atsuyuki/dactyl-manuform-skeleton-edition-4x5/img/image1.png

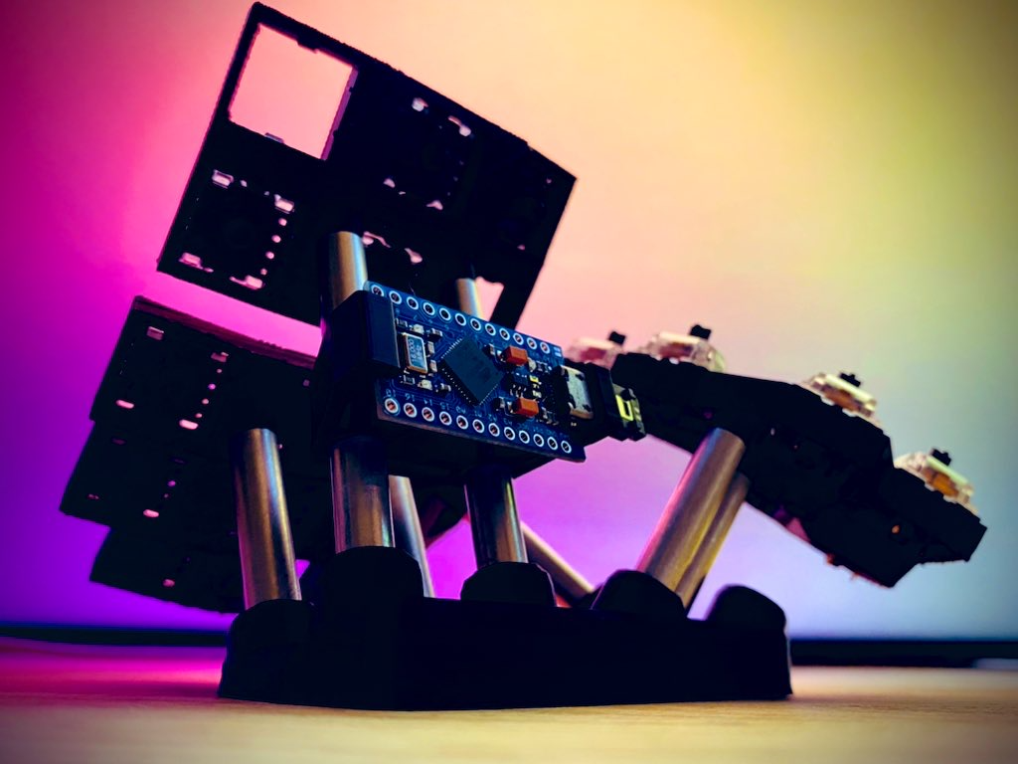
img/image1.png
