atsuyuki/dactyl-manuform-skeleton-edition-4x5/img/image2.png

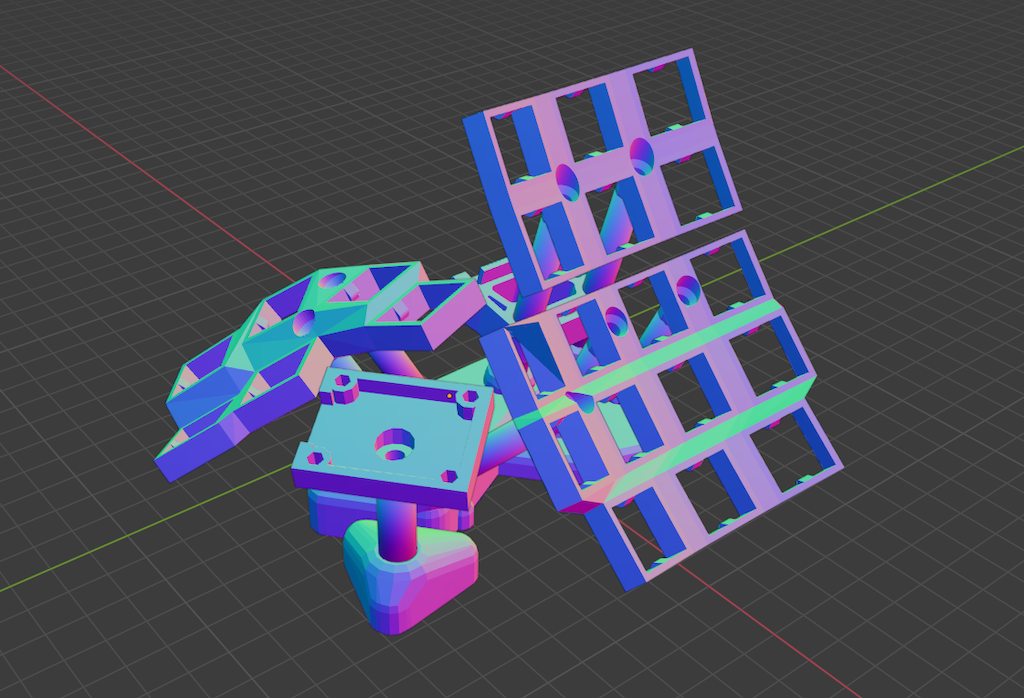
img/image2.png
