atsuyuki/dactyl-manuform-skeleton-edition-4x5/things/right_top.stl

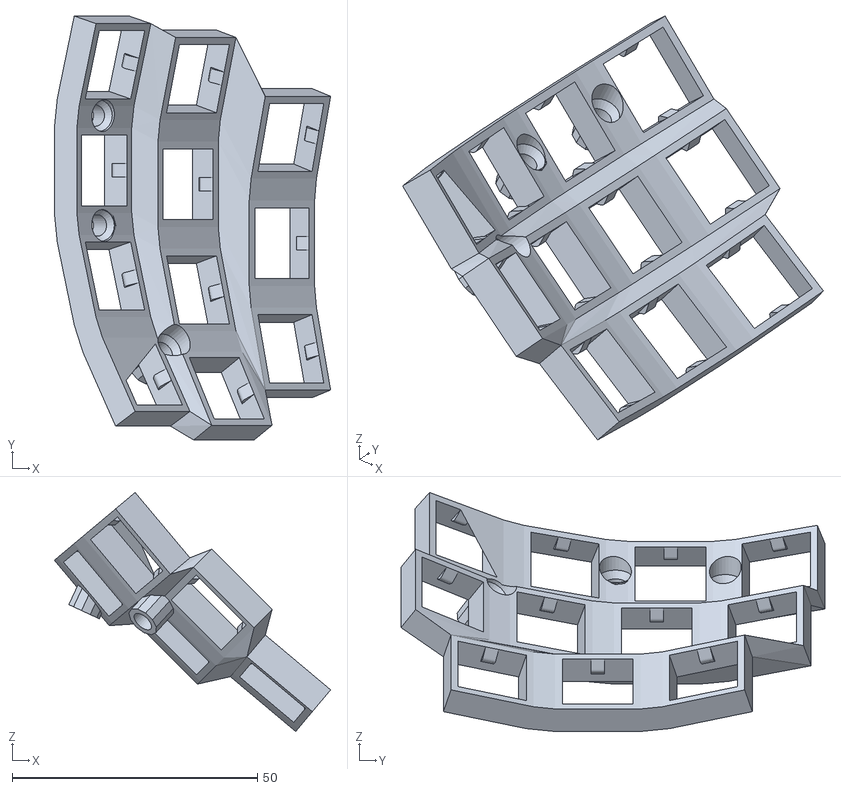
[picture p20: CAD file, 2021-04-04]
things/right_top.stl
56.3 x 86.4 x 48.7
