atsuyuki/dactyl-manuform-skeleton-edition-4x5/source/joystick/right_model.stl

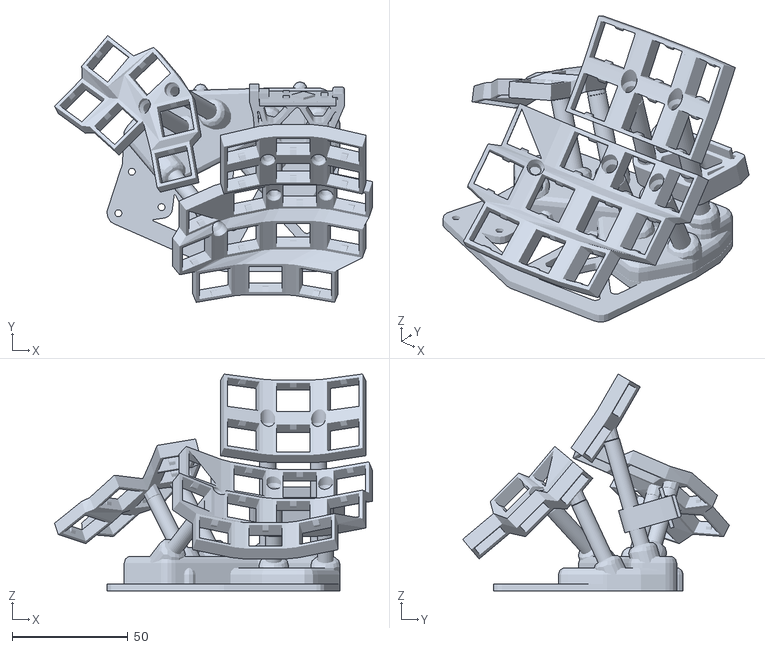
[picture p21: CAD file, 2021-06-23]
source/joystick/right_model.stl
137.5 x 115.4 x 93.8
