atsuyuki/dactyl-manuform-skeleton-edition-4x5/source/things/right-5x6-plate-ready-to-cut.dxf

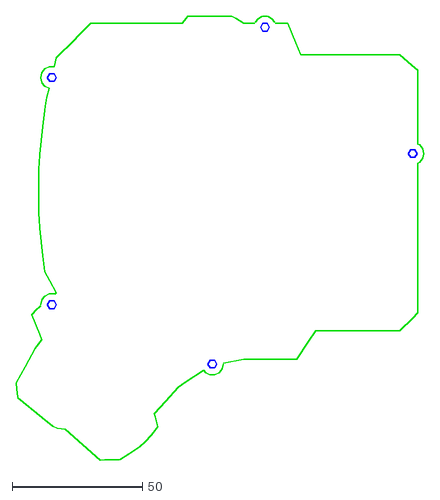
[picture p22: CAD file, 2021-04-20]
source/things/right-5x6-plate-ready-to-cut.dxf
156.5 x 170.5
