atsuyuki/dactyl-manuform-skeleton-edition-4x5/things/right_index.stl

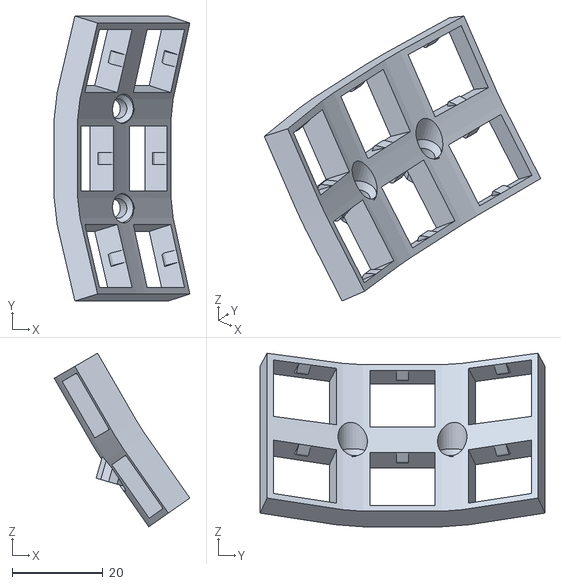
[picture p23: CAD file, 2021-04-04]
things/right_index.stl
30.0 x 63.0 x 38.4
