atsuyuki/dactyl-manuform-skeleton-edition-4x5/source/joystick/clay_model_fixed.stl

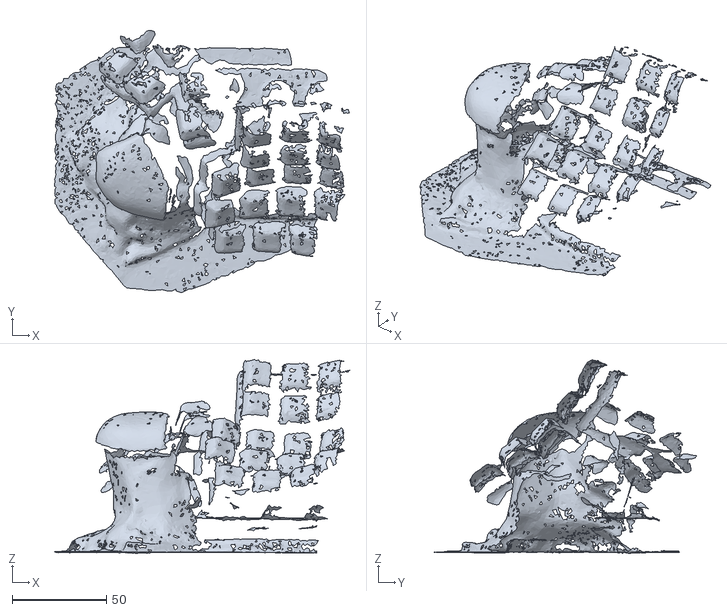
[picture p24: CAD file, 2021-06-23]
source/joystick/clay_model_fixed.stl
156.5 x 139.2 x 103.2
