atsuyuki/dactyl-manuform-skeleton-edition-4x5/source/things/right-4x6-plate.dxf

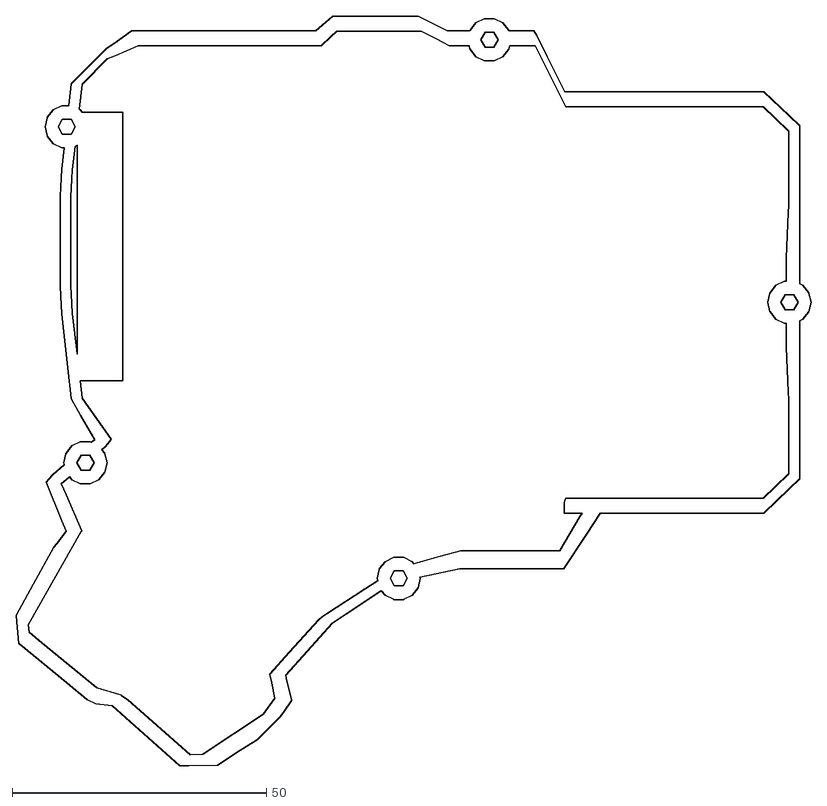
[picture p25: CAD file, 2021-04-20]
source/things/right-4x6-plate.dxf
156.5 x 147.5
