atsuyuki/dactyl-manuform-skeleton-edition-4x5/things/right_bottom.stl

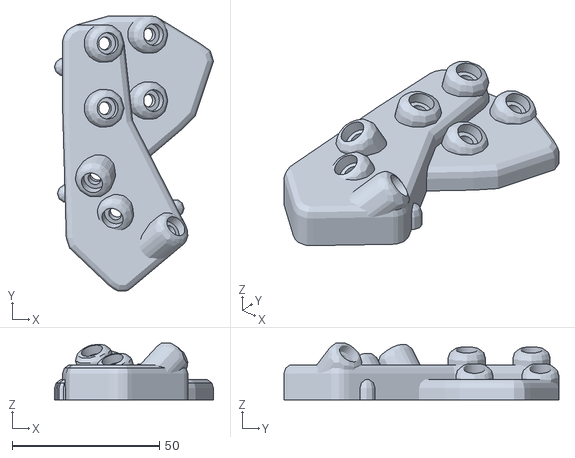
[picture p26: CAD file, 2021-04-04]
things/right_bottom.stl
54.0 x 93.4 x 19.3
