atsuyuki/dactyl-manuform-skeleton-edition-4x5/source/joystick/joystick v10.obj

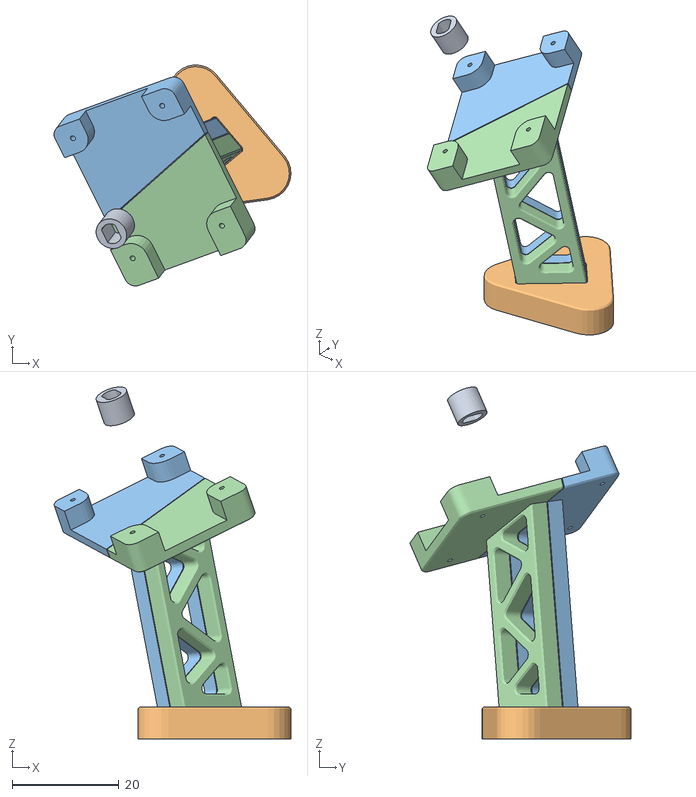
[picture p27: CAD file, 2021-06-23]
source/joystick/joystick v10.obj
44.4 x 41.4 x 66.0
