atsuyuki/dactyl-manuform-skeleton-edition-4x5/source/things/right-plate.dxf

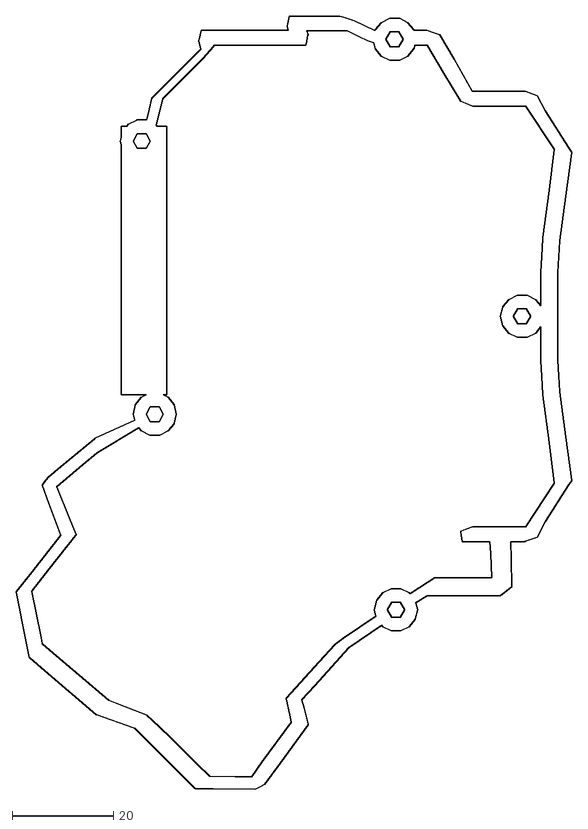
[picture p28: CAD file, 2021-04-20]
source/things/right-plate.dxf
109.4 x 152.3
