atsuyuki/dactyl-manuform-skeleton-edition-4x5/source/things/right-4x5-plate.dxf

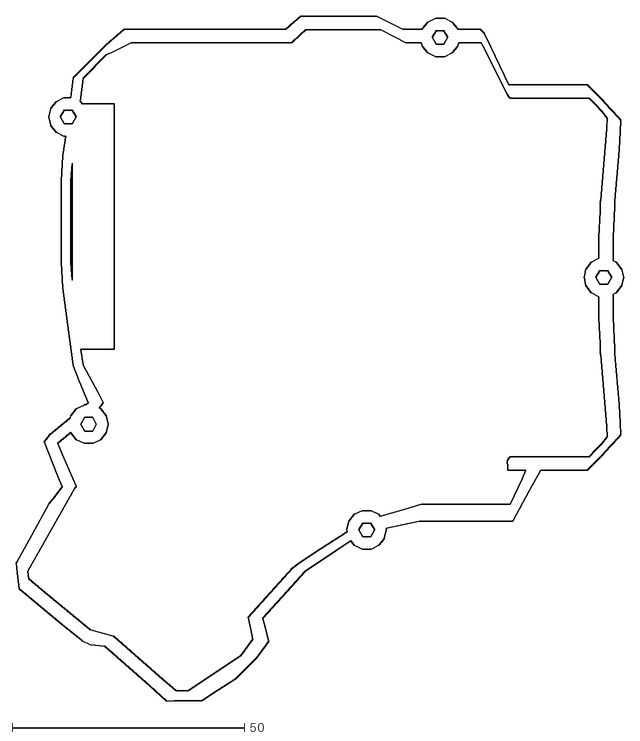
[picture p29: CAD file, 2021-04-20]
source/things/right-4x5-plate.dxf
130.7 x 147.5
