atsuyuki/dactyl-manuform-skeleton-edition-4x5/source/joystick/joystick_bracket_bottom.stl

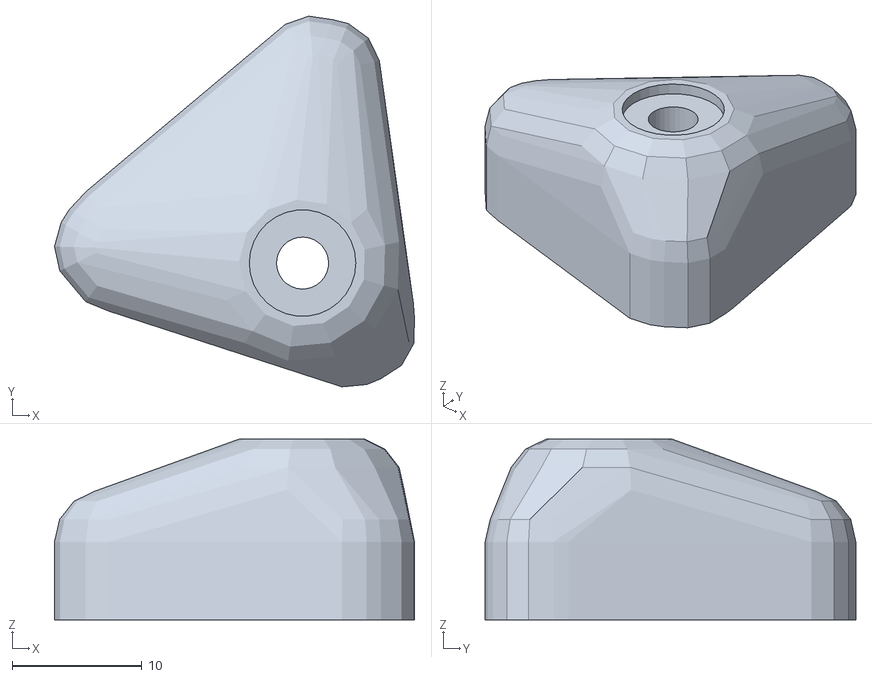
[picture p30: CAD file, 2021-02-26]
source/joystick/joystick_bracket_bottom.stl
27.7 x 28.5 x 13.9
