atsuyuki/dactyl-manuform-skeleton-edition-4x5/source/joystick/joystick_bracket_top.stl

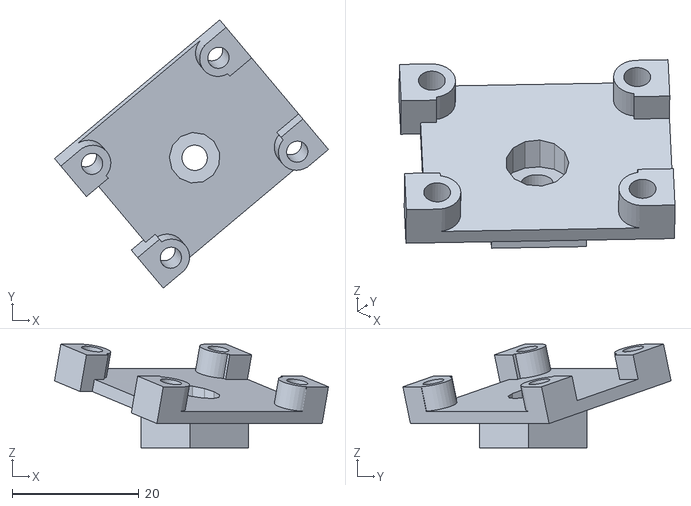
[picture p31: CAD file, 2021-02-26]
source/joystick/joystick_bracket_top.stl
43.2 x 42.3 x 16.4
