atsuyuki/dactyl-manuform-skeleton-edition-4x5/source/things/left_mirror.scad

mirror([1,0,0]){
 import("right_baseplate.stl");
// import("right_bottom.stl");
// import("right_index.stl");
// import("right_thumb.stl");
// import("right_top.stl");
}
