atsuyuki/dactyl-manuform-skeleton-edition-4x5/source/things/right.scad

difference () {
  union () {
    union () {
      translate ([0, 0, 30]) {
        rotate (a=40.0, v=[0, 1, 0]) {
          translate ([0, 0, 0]) {
            translate ([0, 0, 246.80957697923077]) {
              rotate (a=20.0, v=[0, 1, 0]) {
                translate ([0, 0, -246.80957697923077]) {
                  translate ([0, 0, 89.18393769497159]) {
                    rotate (a=14.999999999999998, v=[1, 0, 0]) {
                      translate ([0, 0, -89.18393769497159]) {
                        union () {
                          union () {
                            translate ([0, 7.95, 3]) {
                              cube ([17.4, 1.5, 6], center=true);
                            }
                            translate ([7.95, 0, 3]) {
                              cube ([1.5, 17.4, 6], center=true);
                            }
                            hull () {
                              translate ([7.95, 0, 4.0]) {
                                cube ([1.5, 2.75, 4], center=true);
                              }
                              translate ([7.2, 0, 3.5]) {
                                rotate (a=90.0, v=[1, 0, 0]) {
                                  cylinder ($fn=30, h=2.75, r=0.95, center=true);
                                }
                              }
                            }
                          }
                          mirror ([0, 1, 0]) {
                            mirror ([1, 0, 0]) {
                              union () {
                                translate ([0, 7.95, 3]) {
                                  cube ([17.4, 1.5, 6], center=true);
                                }
                                translate ([7.95, 0, 3]) {
                                  cube ([1.5, 17.4, 6], center=true);
                                }
                                hull () {
                                  translate ([7.95, 0, 4.0]) {
                                    cube ([1.5, 2.75, 4], center=true);
                                  }
                                  translate ([7.2, 0, 3.5]) {
                                    rotate (a=90.0, v=[1, 0, 0]) {
                                      cylinder ($fn=30, h=2.75, r=0.95, center=true);
                                    }
                                  }
                                }
                              }
                            }
                          }
                        }
                      }
                    }
                  }
                }
              }
            }
          }
        }
      }
      translate ([0, 0, 30]) {
        rotate (a=40.0, v=[0, 1, 0]) {
          translate ([0, 0, 0]) {
            translate ([0, 0, 246.80957697923077]) {
              rotate (a=20.0, v=[0, 1, 0]) {
                translate ([0, 0, -246.80957697923077]) {
                  translate ([0, 0, 89.18393769497159]) {
                    rotate (a=0.0, v=[1, 0, 0]) {
                      translate ([0, 0, -89.18393769497159]) {
                        union () {
                          union () {
                            translate ([0, 7.95, 3]) {
                              cube ([17.4, 1.5, 6], center=true);
                            }
                            translate ([7.95, 0, 3]) {
                              cube ([1.5, 17.4, 6], center=true);
                            }
                            hull () {
                              translate ([7.95, 0, 4.0]) {
                                cube ([1.5, 2.75, 4], center=true);
                              }
                              translate ([7.2, 0, 3.5]) {
                                rotate (a=90.0, v=[1, 0, 0]) {
                                  cylinder ($fn=30, h=2.75, r=0.95, center=true);
                                }
                              }
                            }
                          }
                          mirror ([0, 1, 0]) {
                            mirror ([1, 0, 0]) {
                              union () {
                                translate ([0, 7.95, 3]) {
                                  cube ([17.4, 1.5, 6], center=true);
                                }
                                translate ([7.95, 0, 3]) {
                                  cube ([1.5, 17.4, 6], center=true);
                                }
                                hull () {
                                  translate ([7.95, 0, 4.0]) {
                                    cube ([1.5, 2.75, 4], center=true);
                                  }
                                  translate ([7.2, 0, 3.5]) {
                                    rotate (a=90.0, v=[1, 0, 0]) {
                                      cylinder ($fn=30, h=2.75, r=0.95, center=true);
                                    }
                                  }
                                }
                              }
                            }
                          }
                        }
                      }
                    }
                  }
                }
              }
            }
          }
        }
      }
      translate ([0, 0, 30]) {
        rotate (a=40.0, v=[0, 1, 0]) {
          translate ([0, 0, 0]) {
            translate ([0, 0, 246.80957697923077]) {
              rotate (a=20.0, v=[0, 1, 0]) {
                translate ([0, 0, -246.80957697923077]) {
                  translate ([0, 0, 89.18393769497159]) {
                    rotate (a=-14.999999999999998, v=[1, 0, 0]) {
                      translate ([0, 0, -89.18393769497159]) {
                        union () {
                          union () {
                            translate ([0, 7.95, 3]) {
                              cube ([17.4, 1.5, 6], center=true);
                            }
                            translate ([7.95, 0, 3]) {
                              cube ([1.5, 17.4, 6], center=true);
                            }
                            hull () {
                              translate ([7.95, 0, 4.0]) {
                                cube ([1.5, 2.75, 4], center=true);
                              }
                              translate ([7.2, 0, 3.5]) {
                                rotate (a=90.0, v=[1, 0, 0]) {
                                  cylinder ($fn=30, h=2.75, r=0.95, center=true);
                                }
                              }
                            }
                          }
                          mirror ([0, 1, 0]) {
                            mirror ([1, 0, 0]) {
                              union () {
                                translate ([0, 7.95, 3]) {
                                  cube ([17.4, 1.5, 6], center=true);
                                }
                                translate ([7.95, 0, 3]) {
                                  cube ([1.5, 17.4, 6], center=true);
                                }
                                hull () {
                                  translate ([7.95, 0, 4.0]) {
                                    cube ([1.5, 2.75, 4], center=true);
                                  }
                                  translate ([7.2, 0, 3.5]) {
                                    rotate (a=90.0, v=[1, 0, 0]) {
                                      cylinder ($fn=30, h=2.75, r=0.95, center=true);
                                    }
                                  }
                                }
                              }
                            }
                          }
                        }
                      }
                    }
                  }
                }
              }
            }
          }
        }
      }
      translate ([0, 0, 30]) {
        rotate (a=40.0, v=[0, 1, 0]) {
          translate ([0, 0, 0]) {
            translate ([0, 0, 246.80957697923077]) {
              rotate (a=14.999999999999998, v=[0, 1, 0]) {
                translate ([0, 0, -246.80957697923077]) {
                  translate ([0, 0, 89.18393769497159]) {
                    rotate (a=14.999999999999998, v=[1, 0, 0]) {
                      translate ([0, 0, -89.18393769497159]) {
                        union () {
                          union () {
                            translate ([0, 7.95, 3]) {
                              cube ([17.4, 1.5, 6], center=true);
                            }
                            translate ([7.95, 0, 3]) {
                              cube ([1.5, 17.4, 6], center=true);
                            }
                            hull () {
                              translate ([7.95, 0, 4.0]) {
                                cube ([1.5, 2.75, 4], center=true);
                              }
                              translate ([7.2, 0, 3.5]) {
                                rotate (a=90.0, v=[1, 0, 0]) {
                                  cylinder ($fn=30, h=2.75, r=0.95, center=true);
                                }
                              }
                            }
                          }
                          mirror ([0, 1, 0]) {
                            mirror ([1, 0, 0]) {
                              union () {
                                translate ([0, 7.95, 3]) {
                                  cube ([17.4, 1.5, 6], center=true);
                                }
                                translate ([7.95, 0, 3]) {
                                  cube ([1.5, 17.4, 6], center=true);
                                }
                                hull () {
                                  translate ([7.95, 0, 4.0]) {
                                    cube ([1.5, 2.75, 4], center=true);
                                  }
                                  translate ([7.2, 0, 3.5]) {
                                    rotate (a=90.0, v=[1, 0, 0]) {
                                      cylinder ($fn=30, h=2.75, r=0.95, center=true);
                                    }
                                  }
                                }
                              }
                            }
                          }
                        }
                      }
                    }
                  }
                }
              }
            }
          }
        }
      }
      translate ([0, 0, 30]) {
        rotate (a=40.0, v=[0, 1, 0]) {
          translate ([0, 0, 0]) {
            translate ([0, 0, 246.80957697923077]) {
              rotate (a=14.999999999999998, v=[0, 1, 0]) {
                translate ([0, 0, -246.80957697923077]) {
                  translate ([0, 0, 89.18393769497159]) {
                    rotate (a=0.0, v=[1, 0, 0]) {
                      translate ([0, 0, -89.18393769497159]) {
                        union () {
                          union () {
                            translate ([0, 7.95, 3]) {
                              cube ([17.4, 1.5, 6], center=true);
                            }
                            translate ([7.95, 0, 3]) {
                              cube ([1.5, 17.4, 6], center=true);
                            }
                            hull () {
                              translate ([7.95, 0, 4.0]) {
                                cube ([1.5, 2.75, 4], center=true);
                              }
                              translate ([7.2, 0, 3.5]) {
                                rotate (a=90.0, v=[1, 0, 0]) {
                                  cylinder ($fn=30, h=2.75, r=0.95, center=true);
                                }
                              }
                            }
                          }
                          mirror ([0, 1, 0]) {
                            mirror ([1, 0, 0]) {
                              union () {
                                translate ([0, 7.95, 3]) {
                                  cube ([17.4, 1.5, 6], center=true);
                                }
                                translate ([7.95, 0, 3]) {
                                  cube ([1.5, 17.4, 6], center=true);
                                }
                                hull () {
                                  translate ([7.95, 0, 4.0]) {
                                    cube ([1.5, 2.75, 4], center=true);
                                  }
                                  translate ([7.2, 0, 3.5]) {
                                    rotate (a=90.0, v=[1, 0, 0]) {
                                      cylinder ($fn=30, h=2.75, r=0.95, center=true);
                                    }
                                  }
                                }
                              }
                            }
                          }
                        }
                      }
                    }
                  }
                }
              }
            }
          }
        }
      }
      translate ([0, 0, 30]) {
        rotate (a=40.0, v=[0, 1, 0]) {
          translate ([0, 0, 0]) {
            translate ([0, 0, 246.80957697923077]) {
              rotate (a=14.999999999999998, v=[0, 1, 0]) {
                translate ([0, 0, -246.80957697923077]) {
                  translate ([0, 0, 89.18393769497159]) {
                    rotate (a=-14.999999999999998, v=[1, 0, 0]) {
                      translate ([0, 0, -89.18393769497159]) {
                        union () {
                          union () {
                            translate ([0, 7.95, 3]) {
                              cube ([17.4, 1.5, 6], center=true);
                            }
                            translate ([7.95, 0, 3]) {
                              cube ([1.5, 17.4, 6], center=true);
                            }
                            hull () {
                              translate ([7.95, 0, 4.0]) {
                                cube ([1.5, 2.75, 4], center=true);
                              }
                              translate ([7.2, 0, 3.5]) {
                                rotate (a=90.0, v=[1, 0, 0]) {
                                  cylinder ($fn=30, h=2.75, r=0.95, center=true);
                                }
                              }
                            }
                          }
                          mirror ([0, 1, 0]) {
                            mirror ([1, 0, 0]) {
                              union () {
                                translate ([0, 7.95, 3]) {
                                  cube ([17.4, 1.5, 6], center=true);
                                }
                                translate ([7.95, 0, 3]) {
                                  cube ([1.5, 17.4, 6], center=true);
                                }
                                hull () {
                                  translate ([7.95, 0, 4.0]) {
                                    cube ([1.5, 2.75, 4], center=true);
                                  }
                                  translate ([7.2, 0, 3.5]) {
                                    rotate (a=90.0, v=[1, 0, 0]) {
                                      cylinder ($fn=30, h=2.75, r=0.95, center=true);
                                    }
                                  }
                                }
                              }
                            }
                          }
                        }
                      }
                    }
                  }
                }
              }
            }
          }
        }
      }
      translate ([0, 0, 30]) {
        rotate (a=40.0, v=[0, 1, 0]) {
          translate ([0, 2.82, -4.5]) {
            translate ([0, 0, 246.80957697923077]) {
              rotate (a=10.0, v=[0, 1, 0]) {
                translate ([0, 0, -246.80957697923077]) {
                  translate ([0, 0, 89.18393769497159]) {
                    rotate (a=14.999999999999998, v=[1, 0, 0]) {
                      translate ([0, 0, -89.18393769497159]) {
                        union () {
                          union () {
                            translate ([0, 7.95, 3]) {
                              cube ([17.4, 1.5, 6], center=true);
                            }
                            translate ([7.95, 0, 3]) {
                              cube ([1.5, 17.4, 6], center=true);
                            }
                            hull () {
                              translate ([7.95, 0, 4.0]) {
                                cube ([1.5, 2.75, 4], center=true);
                              }
                              translate ([7.2, 0, 3.5]) {
                                rotate (a=90.0, v=[1, 0, 0]) {
                                  cylinder ($fn=30, h=2.75, r=0.95, center=true);
                                }
                              }
                            }
                          }
                          mirror ([0, 1, 0]) {
                            mirror ([1, 0, 0]) {
                              union () {
                                translate ([0, 7.95, 3]) {
                                  cube ([17.4, 1.5, 6], center=true);
                                }
                                translate ([7.95, 0, 3]) {
                                  cube ([1.5, 17.4, 6], center=true);
                                }
                                hull () {
                                  translate ([7.95, 0, 4.0]) {
                                    cube ([1.5, 2.75, 4], center=true);
                                  }
                                  translate ([7.2, 0, 3.5]) {
                                    rotate (a=90.0, v=[1, 0, 0]) {
                                      cylinder ($fn=30, h=2.75, r=0.95, center=true);
                                    }
                                  }
                                }
                              }
                            }
                          }
                        }
                      }
                    }
                  }
                }
              }
            }
          }
        }
      }
      translate ([0, 0, 30]) {
        rotate (a=40.0, v=[0, 1, 0]) {
          translate ([0, 2.82, -4.5]) {
            translate ([0, 0, 246.80957697923077]) {
              rotate (a=10.0, v=[0, 1, 0]) {
                translate ([0, 0, -246.80957697923077]) {
                  translate ([0, 0, 89.18393769497159]) {
                    rotate (a=0.0, v=[1, 0, 0]) {
                      translate ([0, 0, -89.18393769497159]) {
                        union () {
                          union () {
                            translate ([0, 7.95, 3]) {
                              cube ([17.4, 1.5, 6], center=true);
                            }
                            translate ([7.95, 0, 3]) {
                              cube ([1.5, 17.4, 6], center=true);
                            }
                            hull () {
                              translate ([7.95, 0, 4.0]) {
                                cube ([1.5, 2.75, 4], center=true);
                              }
                              translate ([7.2, 0, 3.5]) {
                                rotate (a=90.0, v=[1, 0, 0]) {
                                  cylinder ($fn=30, h=2.75, r=0.95, center=true);
                                }
                              }
                            }
                          }
                          mirror ([0, 1, 0]) {
                            mirror ([1, 0, 0]) {
                              union () {
                                translate ([0, 7.95, 3]) {
                                  cube ([17.4, 1.5, 6], center=true);
                                }
                                translate ([7.95, 0, 3]) {
                                  cube ([1.5, 17.4, 6], center=true);
                                }
                                hull () {
                                  translate ([7.95, 0, 4.0]) {
                                    cube ([1.5, 2.75, 4], center=true);
                                  }
                                  translate ([7.2, 0, 3.5]) {
                                    rotate (a=90.0, v=[1, 0, 0]) {
                                      cylinder ($fn=30, h=2.75, r=0.95, center=true);
                                    }
                                  }
                                }
                              }
                            }
                          }
                        }
                      }
                    }
                  }
                }
              }
            }
          }
        }
      }
      translate ([0, 0, 30]) {
        rotate (a=40.0, v=[0, 1, 0]) {
          translate ([0, 2.82, -4.5]) {
            translate ([0, 0, 246.80957697923077]) {
              rotate (a=10.0, v=[0, 1, 0]) {
                translate ([0, 0, -246.80957697923077]) {
                  translate ([0, 0, 89.18393769497159]) {
                    rotate (a=-14.999999999999998, v=[1, 0, 0]) {
                      translate ([0, 0, -89.18393769497159]) {
                        union () {
                          union () {
                            translate ([0, 7.95, 3]) {
                              cube ([17.4, 1.5, 6], center=true);
                            }
                            translate ([7.95, 0, 3]) {
                              cube ([1.5, 17.4, 6], center=true);
                            }
                            hull () {
                              translate ([7.95, 0, 4.0]) {
                                cube ([1.5, 2.75, 4], center=true);
                              }
                              translate ([7.2, 0, 3.5]) {
                                rotate (a=90.0, v=[1, 0, 0]) {
                                  cylinder ($fn=30, h=2.75, r=0.95, center=true);
                                }
                              }
                            }
                          }
                          mirror ([0, 1, 0]) {
                            mirror ([1, 0, 0]) {
                              union () {
                                translate ([0, 7.95, 3]) {
                                  cube ([17.4, 1.5, 6], center=true);
                                }
                                translate ([7.95, 0, 3]) {
                                  cube ([1.5, 17.4, 6], center=true);
                                }
                                hull () {
                                  translate ([7.95, 0, 4.0]) {
                                    cube ([1.5, 2.75, 4], center=true);
                                  }
                                  translate ([7.2, 0, 3.5]) {
                                    rotate (a=90.0, v=[1, 0, 0]) {
                                      cylinder ($fn=30, h=2.75, r=0.95, center=true);
                                    }
                                  }
                                }
                              }
                            }
                          }
                        }
                      }
                    }
                  }
                }
              }
            }
          }
        }
      }
      translate ([0, 0, 30]) {
        rotate (a=40.0, v=[0, 1, 0]) {
          translate ([0, 2.82, -4.5]) {
            translate ([0, 0, 246.80957697923077]) {
              rotate (a=10.0, v=[0, 1, 0]) {
                translate ([0, 0, -246.80957697923077]) {
                  translate ([0, 0, 89.18393769497159]) {
                    rotate (a=-29.999999999999996, v=[1, 0, 0]) {
                      translate ([0, 0, -89.18393769497159]) {
                        union () {
                          union () {
                            translate ([0, 7.95, 3]) {
                              cube ([17.4, 1.5, 6], center=true);
                            }
                            translate ([7.95, 0, 3]) {
                              cube ([1.5, 17.4, 6], center=true);
                            }
                            hull () {
                              translate ([7.95, 0, 4.0]) {
                                cube ([1.5, 2.75, 4], center=true);
                              }
                              translate ([7.2, 0, 3.5]) {
                                rotate (a=90.0, v=[1, 0, 0]) {
                                  cylinder ($fn=30, h=2.75, r=0.95, center=true);
                                }
                              }
                            }
                          }
                          mirror ([0, 1, 0]) {
                            mirror ([1, 0, 0]) {
                              union () {
                                translate ([0, 7.95, 3]) {
                                  cube ([17.4, 1.5, 6], center=true);
                                }
                                translate ([7.95, 0, 3]) {
                                  cube ([1.5, 17.4, 6], center=true);
                                }
                                hull () {
                                  translate ([7.95, 0, 4.0]) {
                                    cube ([1.5, 2.75, 4], center=true);
                                  }
                                  translate ([7.2, 0, 3.5]) {
                                    rotate (a=90.0, v=[1, 0, 0]) {
                                      cylinder ($fn=30, h=2.75, r=0.95, center=true);
                                    }
                                  }
                                }
                              }
                            }
                          }
                        }
                      }
                    }
                  }
                }
              }
            }
          }
        }
      }
      translate ([0, 0, 30]) {
        rotate (a=40.0, v=[0, 1, 0]) {
          translate ([0, 0, 0]) {
            translate ([0, 0, 246.80957697923077]) {
              rotate (a=5.0, v=[0, 1, 0]) {
                translate ([0, 0, -246.80957697923077]) {
                  translate ([0, 0, 89.18393769497159]) {
                    rotate (a=14.999999999999998, v=[1, 0, 0]) {
                      translate ([0, 0, -89.18393769497159]) {
                        union () {
                          union () {
                            translate ([0, 7.95, 3]) {
                              cube ([17.4, 1.5, 6], center=true);
                            }
                            translate ([7.95, 0, 3]) {
                              cube ([1.5, 17.4, 6], center=true);
                            }
                            hull () {
                              translate ([7.95, 0, 4.0]) {
                                cube ([1.5, 2.75, 4], center=true);
                              }
                              translate ([7.2, 0, 3.5]) {
                                rotate (a=90.0, v=[1, 0, 0]) {
                                  cylinder ($fn=30, h=2.75, r=0.95, center=true);
                                }
                              }
                            }
                          }
                          mirror ([0, 1, 0]) {
                            mirror ([1, 0, 0]) {
                              union () {
                                translate ([0, 7.95, 3]) {
                                  cube ([17.4, 1.5, 6], center=true);
                                }
                                translate ([7.95, 0, 3]) {
                                  cube ([1.5, 17.4, 6], center=true);
                                }
                                hull () {
                                  translate ([7.95, 0, 4.0]) {
                                    cube ([1.5, 2.75, 4], center=true);
                                  }
                                  translate ([7.2, 0, 3.5]) {
                                    rotate (a=90.0, v=[1, 0, 0]) {
                                      cylinder ($fn=30, h=2.75, r=0.95, center=true);
                                    }
                                  }
                                }
                              }
                            }
                          }
                        }
                      }
                    }
                  }
                }
              }
            }
          }
        }
      }
      translate ([0, 0, 30]) {
        rotate (a=40.0, v=[0, 1, 0]) {
          translate ([0, 0, 0]) {
            translate ([0, 0, 246.80957697923077]) {
              rotate (a=5.0, v=[0, 1, 0]) {
                translate ([0, 0, -246.80957697923077]) {
                  translate ([0, 0, 89.18393769497159]) {
                    rotate (a=0.0, v=[1, 0, 0]) {
                      translate ([0, 0, -89.18393769497159]) {
                        union () {
                          union () {
                            translate ([0, 7.95, 3]) {
                              cube ([17.4, 1.5, 6], center=true);
                            }
                            translate ([7.95, 0, 3]) {
                              cube ([1.5, 17.4, 6], center=true);
                            }
                            hull () {
                              translate ([7.95, 0, 4.0]) {
                                cube ([1.5, 2.75, 4], center=true);
                              }
                              translate ([7.2, 0, 3.5]) {
                                rotate (a=90.0, v=[1, 0, 0]) {
                                  cylinder ($fn=30, h=2.75, r=0.95, center=true);
                                }
                              }
                            }
                          }
                          mirror ([0, 1, 0]) {
                            mirror ([1, 0, 0]) {
                              union () {
                                translate ([0, 7.95, 3]) {
                                  cube ([17.4, 1.5, 6], center=true);
                                }
                                translate ([7.95, 0, 3]) {
                                  cube ([1.5, 17.4, 6], center=true);
                                }
                                hull () {
                                  translate ([7.95, 0, 4.0]) {
                                    cube ([1.5, 2.75, 4], center=true);
                                  }
                                  translate ([7.2, 0, 3.5]) {
                                    rotate (a=90.0, v=[1, 0, 0]) {
                                      cylinder ($fn=30, h=2.75, r=0.95, center=true);
                                    }
                                  }
                                }
                              }
                            }
                          }
                        }
                      }
                    }
                  }
                }
              }
            }
          }
        }
      }
      translate ([0, 0, 30]) {
        rotate (a=40.0, v=[0, 1, 0]) {
          translate ([0, 0, 0]) {
            translate ([0, 0, 246.80957697923077]) {
              rotate (a=5.0, v=[0, 1, 0]) {
                translate ([0, 0, -246.80957697923077]) {
                  translate ([0, 0, 89.18393769497159]) {
                    rotate (a=-14.999999999999998, v=[1, 0, 0]) {
                      translate ([0, 0, -89.18393769497159]) {
                        union () {
                          union () {
                            translate ([0, 7.95, 3]) {
                              cube ([17.4, 1.5, 6], center=true);
                            }
                            translate ([7.95, 0, 3]) {
                              cube ([1.5, 17.4, 6], center=true);
                            }
                            hull () {
                              translate ([7.95, 0, 4.0]) {
                                cube ([1.5, 2.75, 4], center=true);
                              }
                              translate ([7.2, 0, 3.5]) {
                                rotate (a=90.0, v=[1, 0, 0]) {
                                  cylinder ($fn=30, h=2.75, r=0.95, center=true);
                                }
                              }
                            }
                          }
                          mirror ([0, 1, 0]) {
                            mirror ([1, 0, 0]) {
                              union () {
                                translate ([0, 7.95, 3]) {
                                  cube ([17.4, 1.5, 6], center=true);
                                }
                                translate ([7.95, 0, 3]) {
                                  cube ([1.5, 17.4, 6], center=true);
                                }
                                hull () {
                                  translate ([7.95, 0, 4.0]) {
                                    cube ([1.5, 2.75, 4], center=true);
                                  }
                                  translate ([7.2, 0, 3.5]) {
                                    rotate (a=90.0, v=[1, 0, 0]) {
                                      cylinder ($fn=30, h=2.75, r=0.95, center=true);
                                    }
                                  }
                                }
                              }
                            }
                          }
                        }
                      }
                    }
                  }
                }
              }
            }
          }
        }
      }
      translate ([0, 0, 30]) {
        rotate (a=40.0, v=[0, 1, 0]) {
          translate ([0, 0, 0]) {
            translate ([0, 0, 246.80957697923077]) {
              rotate (a=5.0, v=[0, 1, 0]) {
                translate ([0, 0, -246.80957697923077]) {
                  translate ([0, 0, 89.18393769497159]) {
                    rotate (a=-29.999999999999996, v=[1, 0, 0]) {
                      translate ([0, 0, -89.18393769497159]) {
                        union () {
                          union () {
                            translate ([0, 7.95, 3]) {
                              cube ([17.4, 1.5, 6], center=true);
                            }
                            translate ([7.95, 0, 3]) {
                              cube ([1.5, 17.4, 6], center=true);
                            }
                            hull () {
                              translate ([7.95, 0, 4.0]) {
                                cube ([1.5, 2.75, 4], center=true);
                              }
                              translate ([7.2, 0, 3.5]) {
                                rotate (a=90.0, v=[1, 0, 0]) {
                                  cylinder ($fn=30, h=2.75, r=0.95, center=true);
                                }
                              }
                            }
                          }
                          mirror ([0, 1, 0]) {
                            mirror ([1, 0, 0]) {
                              union () {
                                translate ([0, 7.95, 3]) {
                                  cube ([17.4, 1.5, 6], center=true);
                                }
                                translate ([7.95, 0, 3]) {
                                  cube ([1.5, 17.4, 6], center=true);
                                }
                                hull () {
                                  translate ([7.95, 0, 4.0]) {
                                    cube ([1.5, 2.75, 4], center=true);
                                  }
                                  translate ([7.2, 0, 3.5]) {
                                    rotate (a=90.0, v=[1, 0, 0]) {
                                      cylinder ($fn=30, h=2.75, r=0.95, center=true);
                                    }
                                  }
                                }
                              }
                            }
                          }
                        }
                      }
                    }
                  }
                }
              }
            }
          }
        }
      }
      translate ([0, 0, 30]) {
        rotate (a=40.0, v=[0, 1, 0]) {
          translate ([0, -12, 5.64]) {
            translate ([0, 0, 246.80957697923077]) {
              rotate (a=0.0, v=[0, 1, 0]) {
                translate ([0, 0, -246.80957697923077]) {
                  translate ([0, 0, 89.18393769497159]) {
                    rotate (a=14.999999999999998, v=[1, 0, 0]) {
                      translate ([0, 0, -89.18393769497159]) {
                        union () {
                          union () {
                            translate ([0, 7.95, 3]) {
                              cube ([17.4, 1.5, 6], center=true);
                            }
                            translate ([7.95, 0, 3]) {
                              cube ([1.5, 17.4, 6], center=true);
                            }
                            hull () {
                              translate ([7.95, 0, 4.0]) {
                                cube ([1.5, 2.75, 4], center=true);
                              }
                              translate ([7.2, 0, 3.5]) {
                                rotate (a=90.0, v=[1, 0, 0]) {
                                  cylinder ($fn=30, h=2.75, r=0.95, center=true);
                                }
                              }
                            }
                          }
                          mirror ([0, 1, 0]) {
                            mirror ([1, 0, 0]) {
                              union () {
                                translate ([0, 7.95, 3]) {
                                  cube ([17.4, 1.5, 6], center=true);
                                }
                                translate ([7.95, 0, 3]) {
                                  cube ([1.5, 17.4, 6], center=true);
                                }
                                hull () {
                                  translate ([7.95, 0, 4.0]) {
                                    cube ([1.5, 2.75, 4], center=true);
                                  }
                                  translate ([7.2, 0, 3.5]) {
                                    rotate (a=90.0, v=[1, 0, 0]) {
                                      cylinder ($fn=30, h=2.75, r=0.95, center=true);
                                    }
                                  }
                                }
                              }
                            }
                          }
                        }
                      }
                    }
                  }
                }
              }
            }
          }
        }
      }
      translate ([0, 0, 30]) {
        rotate (a=40.0, v=[0, 1, 0]) {
          translate ([0, -12, 5.64]) {
            translate ([0, 0, 246.80957697923077]) {
              rotate (a=0.0, v=[0, 1, 0]) {
                translate ([0, 0, -246.80957697923077]) {
                  translate ([0, 0, 89.18393769497159]) {
                    rotate (a=0.0, v=[1, 0, 0]) {
                      translate ([0, 0, -89.18393769497159]) {
                        union () {
                          union () {
                            translate ([0, 7.95, 3]) {
                              cube ([17.4, 1.5, 6], center=true);
                            }
                            translate ([7.95, 0, 3]) {
                              cube ([1.5, 17.4, 6], center=true);
                            }
                            hull () {
                              translate ([7.95, 0, 4.0]) {
                                cube ([1.5, 2.75, 4], center=true);
                              }
                              translate ([7.2, 0, 3.5]) {
                                rotate (a=90.0, v=[1, 0, 0]) {
                                  cylinder ($fn=30, h=2.75, r=0.95, center=true);
                                }
                              }
                            }
                          }
                          mirror ([0, 1, 0]) {
                            mirror ([1, 0, 0]) {
                              union () {
                                translate ([0, 7.95, 3]) {
                                  cube ([17.4, 1.5, 6], center=true);
                                }
                                translate ([7.95, 0, 3]) {
                                  cube ([1.5, 17.4, 6], center=true);
                                }
                                hull () {
                                  translate ([7.95, 0, 4.0]) {
                                    cube ([1.5, 2.75, 4], center=true);
                                  }
                                  translate ([7.2, 0, 3.5]) {
                                    rotate (a=90.0, v=[1, 0, 0]) {
                                      cylinder ($fn=30, h=2.75, r=0.95, center=true);
                                    }
                                  }
                                }
                              }
                            }
                          }
                        }
                      }
                    }
                  }
                }
              }
            }
          }
        }
      }
      translate ([0, 0, 30]) {
        rotate (a=40.0, v=[0, 1, 0]) {
          translate ([0, -12, 5.64]) {
            translate ([0, 0, 246.80957697923077]) {
              rotate (a=0.0, v=[0, 1, 0]) {
                translate ([0, 0, -246.80957697923077]) {
                  translate ([0, 0, 89.18393769497159]) {
                    rotate (a=-14.999999999999998, v=[1, 0, 0]) {
                      translate ([0, 0, -89.18393769497159]) {
                        union () {
                          union () {
                            translate ([0, 7.95, 3]) {
                              cube ([17.4, 1.5, 6], center=true);
                            }
                            translate ([7.95, 0, 3]) {
                              cube ([1.5, 17.4, 6], center=true);
                            }
                            hull () {
                              translate ([7.95, 0, 4.0]) {
                                cube ([1.5, 2.75, 4], center=true);
                              }
                              translate ([7.2, 0, 3.5]) {
                                rotate (a=90.0, v=[1, 0, 0]) {
                                  cylinder ($fn=30, h=2.75, r=0.95, center=true);
                                }
                              }
                            }
                          }
                          mirror ([0, 1, 0]) {
                            mirror ([1, 0, 0]) {
                              union () {
                                translate ([0, 7.95, 3]) {
                                  cube ([17.4, 1.5, 6], center=true);
                                }
                                translate ([7.95, 0, 3]) {
                                  cube ([1.5, 17.4, 6], center=true);
                                }
                                hull () {
                                  translate ([7.95, 0, 4.0]) {
                                    cube ([1.5, 2.75, 4], center=true);
                                  }
                                  translate ([7.2, 0, 3.5]) {
                                    rotate (a=90.0, v=[1, 0, 0]) {
                                      cylinder ($fn=30, h=2.75, r=0.95, center=true);
                                    }
                                  }
                                }
                              }
                            }
                          }
                        }
                      }
                    }
                  }
                }
              }
            }
          }
        }
      }
    }
    union () {
      union () {
        hull () {
          translate ([0, 0, 30]) {
            rotate (a=40.0, v=[0, 1, 0]) {
              translate ([0, 0, 0]) {
                translate ([0, 0, 246.80957697923077]) {
                  rotate (a=14.999999999999998, v=[0, 1, 0]) {
                    translate ([0, 0, -246.80957697923077]) {
                      translate ([0, 0, 89.18393769497159]) {
                        rotate (a=14.999999999999998, v=[1, 0, 0]) {
                          translate ([0, 0, -89.18393769497159]) {
                            translate ([-8.694999999999999, 8.694999999999999, 0]) {
                              translate ([0, 0, 3]) {
                                cube ([0.01, 0.01, 6], center=true);
                              }
                            }
                          }
                        }
                      }
                    }
                  }
                }
              }
            }
          }
          translate ([0, 0, 30]) {
            rotate (a=40.0, v=[0, 1, 0]) {
              translate ([0, 0, 0]) {
                translate ([0, 0, 246.80957697923077]) {
                  rotate (a=20.0, v=[0, 1, 0]) {
                    translate ([0, 0, -246.80957697923077]) {
                      translate ([0, 0, 89.18393769497159]) {
                        rotate (a=14.999999999999998, v=[1, 0, 0]) {
                          translate ([0, 0, -89.18393769497159]) {
                            translate ([8.694999999999999, 8.694999999999999, 0]) {
                              translate ([0, 0, 3]) {
                                cube ([0.01, 0.01, 6], center=true);
                              }
                            }
                          }
                        }
                      }
                    }
                  }
                }
              }
            }
          }
          translate ([0, 0, 30]) {
            rotate (a=40.0, v=[0, 1, 0]) {
              translate ([0, 0, 0]) {
                translate ([0, 0, 246.80957697923077]) {
                  rotate (a=14.999999999999998, v=[0, 1, 0]) {
                    translate ([0, 0, -246.80957697923077]) {
                      translate ([0, 0, 89.18393769497159]) {
                        rotate (a=14.999999999999998, v=[1, 0, 0]) {
                          translate ([0, 0, -89.18393769497159]) {
                            translate ([-8.694999999999999, -8.694999999999999, 0]) {
                              translate ([0, 0, 3]) {
                                cube ([0.01, 0.01, 6], center=true);
                              }
                            }
                          }
                        }
                      }
                    }
                  }
                }
              }
            }
          }
        }
        hull () {
          translate ([0, 0, 30]) {
            rotate (a=40.0, v=[0, 1, 0]) {
              translate ([0, 0, 0]) {
                translate ([0, 0, 246.80957697923077]) {
                  rotate (a=20.0, v=[0, 1, 0]) {
                    translate ([0, 0, -246.80957697923077]) {
                      translate ([0, 0, 89.18393769497159]) {
                        rotate (a=14.999999999999998, v=[1, 0, 0]) {
                          translate ([0, 0, -89.18393769497159]) {
                            translate ([8.694999999999999, 8.694999999999999, 0]) {
                              translate ([0, 0, 3]) {
                                cube ([0.01, 0.01, 6], center=true);
                              }
                            }
                          }
                        }
                      }
                    }
                  }
                }
              }
            }
          }
          translate ([0, 0, 30]) {
            rotate (a=40.0, v=[0, 1, 0]) {
              translate ([0, 0, 0]) {
                translate ([0, 0, 246.80957697923077]) {
                  rotate (a=14.999999999999998, v=[0, 1, 0]) {
                    translate ([0, 0, -246.80957697923077]) {
                      translate ([0, 0, 89.18393769497159]) {
                        rotate (a=14.999999999999998, v=[1, 0, 0]) {
                          translate ([0, 0, -89.18393769497159]) {
                            translate ([-8.694999999999999, -8.694999999999999, 0]) {
                              translate ([0, 0, 3]) {
                                cube ([0.01, 0.01, 6], center=true);
                              }
                            }
                          }
                        }
                      }
                    }
                  }
                }
              }
            }
          }
          translate ([0, 0, 30]) {
            rotate (a=40.0, v=[0, 1, 0]) {
              translate ([0, 0, 0]) {
                translate ([0, 0, 246.80957697923077]) {
                  rotate (a=20.0, v=[0, 1, 0]) {
                    translate ([0, 0, -246.80957697923077]) {
                      translate ([0, 0, 89.18393769497159]) {
                        rotate (a=14.999999999999998, v=[1, 0, 0]) {
                          translate ([0, 0, -89.18393769497159]) {
                            translate ([8.694999999999999, -8.694999999999999, 0]) {
                              translate ([0, 0, 3]) {
                                cube ([0.01, 0.01, 6], center=true);
                              }
                            }
                          }
                        }
                      }
                    }
                  }
                }
              }
            }
          }
        }
      }
      union () {
        hull () {
          translate ([0, 0, 30]) {
            rotate (a=40.0, v=[0, 1, 0]) {
              translate ([0, 0, 0]) {
                translate ([0, 0, 246.80957697923077]) {
                  rotate (a=14.999999999999998, v=[0, 1, 0]) {
                    translate ([0, 0, -246.80957697923077]) {
                      translate ([0, 0, 89.18393769497159]) {
                        rotate (a=0.0, v=[1, 0, 0]) {
                          translate ([0, 0, -89.18393769497159]) {
                            translate ([-8.694999999999999, 8.694999999999999, 0]) {
                              translate ([0, 0, 3]) {
                                cube ([0.01, 0.01, 6], center=true);
                              }
                            }
                          }
                        }
                      }
                    }
                  }
                }
              }
            }
          }
          translate ([0, 0, 30]) {
            rotate (a=40.0, v=[0, 1, 0]) {
              translate ([0, 0, 0]) {
                translate ([0, 0, 246.80957697923077]) {
                  rotate (a=20.0, v=[0, 1, 0]) {
                    translate ([0, 0, -246.80957697923077]) {
                      translate ([0, 0, 89.18393769497159]) {
                        rotate (a=0.0, v=[1, 0, 0]) {
                          translate ([0, 0, -89.18393769497159]) {
                            translate ([8.694999999999999, 8.694999999999999, 0]) {
                              translate ([0, 0, 3]) {
                                cube ([0.01, 0.01, 6], center=true);
                              }
                            }
                          }
                        }
                      }
                    }
                  }
                }
              }
            }
          }
          translate ([0, 0, 30]) {
            rotate (a=40.0, v=[0, 1, 0]) {
              translate ([0, 0, 0]) {
                translate ([0, 0, 246.80957697923077]) {
                  rotate (a=14.999999999999998, v=[0, 1, 0]) {
                    translate ([0, 0, -246.80957697923077]) {
                      translate ([0, 0, 89.18393769497159]) {
                        rotate (a=0.0, v=[1, 0, 0]) {
                          translate ([0, 0, -89.18393769497159]) {
                            translate ([-8.694999999999999, -8.694999999999999, 0]) {
                              translate ([0, 0, 3]) {
                                cube ([0.01, 0.01, 6], center=true);
                              }
                            }
                          }
                        }
                      }
                    }
                  }
                }
              }
            }
          }
        }
        hull () {
          translate ([0, 0, 30]) {
            rotate (a=40.0, v=[0, 1, 0]) {
              translate ([0, 0, 0]) {
                translate ([0, 0, 246.80957697923077]) {
                  rotate (a=20.0, v=[0, 1, 0]) {
                    translate ([0, 0, -246.80957697923077]) {
                      translate ([0, 0, 89.18393769497159]) {
                        rotate (a=0.0, v=[1, 0, 0]) {
                          translate ([0, 0, -89.18393769497159]) {
                            translate ([8.694999999999999, 8.694999999999999, 0]) {
                              translate ([0, 0, 3]) {
                                cube ([0.01, 0.01, 6], center=true);
                              }
                            }
                          }
                        }
                      }
                    }
                  }
                }
              }
            }
          }
          translate ([0, 0, 30]) {
            rotate (a=40.0, v=[0, 1, 0]) {
              translate ([0, 0, 0]) {
                translate ([0, 0, 246.80957697923077]) {
                  rotate (a=14.999999999999998, v=[0, 1, 0]) {
                    translate ([0, 0, -246.80957697923077]) {
                      translate ([0, 0, 89.18393769497159]) {
                        rotate (a=0.0, v=[1, 0, 0]) {
                          translate ([0, 0, -89.18393769497159]) {
                            translate ([-8.694999999999999, -8.694999999999999, 0]) {
                              translate ([0, 0, 3]) {
                                cube ([0.01, 0.01, 6], center=true);
                              }
                            }
                          }
                        }
                      }
                    }
                  }
                }
              }
            }
          }
          translate ([0, 0, 30]) {
            rotate (a=40.0, v=[0, 1, 0]) {
              translate ([0, 0, 0]) {
                translate ([0, 0, 246.80957697923077]) {
                  rotate (a=20.0, v=[0, 1, 0]) {
                    translate ([0, 0, -246.80957697923077]) {
                      translate ([0, 0, 89.18393769497159]) {
                        rotate (a=0.0, v=[1, 0, 0]) {
                          translate ([0, 0, -89.18393769497159]) {
                            translate ([8.694999999999999, -8.694999999999999, 0]) {
                              translate ([0, 0, 3]) {
                                cube ([0.01, 0.01, 6], center=true);
                              }
                            }
                          }
                        }
                      }
                    }
                  }
                }
              }
            }
          }
        }
      }
      union () {
        hull () {
          translate ([0, 0, 30]) {
            rotate (a=40.0, v=[0, 1, 0]) {
              translate ([0, 0, 0]) {
                translate ([0, 0, 246.80957697923077]) {
                  rotate (a=14.999999999999998, v=[0, 1, 0]) {
                    translate ([0, 0, -246.80957697923077]) {
                      translate ([0, 0, 89.18393769497159]) {
                        rotate (a=-14.999999999999998, v=[1, 0, 0]) {
                          translate ([0, 0, -89.18393769497159]) {
                            translate ([-8.694999999999999, 8.694999999999999, 0]) {
                              translate ([0, 0, 3]) {
                                cube ([0.01, 0.01, 6], center=true);
                              }
                            }
                          }
                        }
                      }
                    }
                  }
                }
              }
            }
          }
          translate ([0, 0, 30]) {
            rotate (a=40.0, v=[0, 1, 0]) {
              translate ([0, 0, 0]) {
                translate ([0, 0, 246.80957697923077]) {
                  rotate (a=20.0, v=[0, 1, 0]) {
                    translate ([0, 0, -246.80957697923077]) {
                      translate ([0, 0, 89.18393769497159]) {
                        rotate (a=-14.999999999999998, v=[1, 0, 0]) {
                          translate ([0, 0, -89.18393769497159]) {
                            translate ([8.694999999999999, 8.694999999999999, 0]) {
                              translate ([0, 0, 3]) {
                                cube ([0.01, 0.01, 6], center=true);
                              }
                            }
                          }
                        }
                      }
                    }
                  }
                }
              }
            }
          }
          translate ([0, 0, 30]) {
            rotate (a=40.0, v=[0, 1, 0]) {
              translate ([0, 0, 0]) {
                translate ([0, 0, 246.80957697923077]) {
                  rotate (a=14.999999999999998, v=[0, 1, 0]) {
                    translate ([0, 0, -246.80957697923077]) {
                      translate ([0, 0, 89.18393769497159]) {
                        rotate (a=-14.999999999999998, v=[1, 0, 0]) {
                          translate ([0, 0, -89.18393769497159]) {
                            translate ([-8.694999999999999, -8.694999999999999, 0]) {
                              translate ([0, 0, 3]) {
                                cube ([0.01, 0.01, 6], center=true);
                              }
                            }
                          }
                        }
                      }
                    }
                  }
                }
              }
            }
          }
        }
        hull () {
          translate ([0, 0, 30]) {
            rotate (a=40.0, v=[0, 1, 0]) {
              translate ([0, 0, 0]) {
                translate ([0, 0, 246.80957697923077]) {
                  rotate (a=20.0, v=[0, 1, 0]) {
                    translate ([0, 0, -246.80957697923077]) {
                      translate ([0, 0, 89.18393769497159]) {
                        rotate (a=-14.999999999999998, v=[1, 0, 0]) {
                          translate ([0, 0, -89.18393769497159]) {
                            translate ([8.694999999999999, 8.694999999999999, 0]) {
                              translate ([0, 0, 3]) {
                                cube ([0.01, 0.01, 6], center=true);
                              }
                            }
                          }
                        }
                      }
                    }
                  }
                }
              }
            }
          }
          translate ([0, 0, 30]) {
            rotate (a=40.0, v=[0, 1, 0]) {
              translate ([0, 0, 0]) {
                translate ([0, 0, 246.80957697923077]) {
                  rotate (a=14.999999999999998, v=[0, 1, 0]) {
                    translate ([0, 0, -246.80957697923077]) {
                      translate ([0, 0, 89.18393769497159]) {
                        rotate (a=-14.999999999999998, v=[1, 0, 0]) {
                          translate ([0, 0, -89.18393769497159]) {
                            translate ([-8.694999999999999, -8.694999999999999, 0]) {
                              translate ([0, 0, 3]) {
                                cube ([0.01, 0.01, 6], center=true);
                              }
                            }
                          }
                        }
                      }
                    }
                  }
                }
              }
            }
          }
          translate ([0, 0, 30]) {
            rotate (a=40.0, v=[0, 1, 0]) {
              translate ([0, 0, 0]) {
                translate ([0, 0, 246.80957697923077]) {
                  rotate (a=20.0, v=[0, 1, 0]) {
                    translate ([0, 0, -246.80957697923077]) {
                      translate ([0, 0, 89.18393769497159]) {
                        rotate (a=-14.999999999999998, v=[1, 0, 0]) {
                          translate ([0, 0, -89.18393769497159]) {
                            translate ([8.694999999999999, -8.694999999999999, 0]) {
                              translate ([0, 0, 3]) {
                                cube ([0.01, 0.01, 6], center=true);
                              }
                            }
                          }
                        }
                      }
                    }
                  }
                }
              }
            }
          }
        }
      }
      union () {
        hull () {
          translate ([0, 0, 30]) {
            rotate (a=40.0, v=[0, 1, 0]) {
              translate ([0, 0, 0]) {
                translate ([0, 0, 246.80957697923077]) {
                  rotate (a=5.0, v=[0, 1, 0]) {
                    translate ([0, 0, -246.80957697923077]) {
                      translate ([0, 0, 89.18393769497159]) {
                        rotate (a=14.999999999999998, v=[1, 0, 0]) {
                          translate ([0, 0, -89.18393769497159]) {
                            translate ([-8.694999999999999, 8.694999999999999, 0]) {
                              translate ([0, 0, 3]) {
                                cube ([0.01, 0.01, 6], center=true);
                              }
                            }
                          }
                        }
                      }
                    }
                  }
                }
              }
            }
          }
          translate ([0, 0, 30]) {
            rotate (a=40.0, v=[0, 1, 0]) {
              translate ([0, 2.82, -4.5]) {
                translate ([0, 0, 246.80957697923077]) {
                  rotate (a=10.0, v=[0, 1, 0]) {
                    translate ([0, 0, -246.80957697923077]) {
                      translate ([0, 0, 89.18393769497159]) {
                        rotate (a=14.999999999999998, v=[1, 0, 0]) {
                          translate ([0, 0, -89.18393769497159]) {
                            translate ([8.694999999999999, 8.694999999999999, 0]) {
                              translate ([0, 0, 3]) {
                                cube ([0.01, 0.01, 6], center=true);
                              }
                            }
                          }
                        }
                      }
                    }
                  }
                }
              }
            }
          }
          translate ([0, 0, 30]) {
            rotate (a=40.0, v=[0, 1, 0]) {
              translate ([0, 0, 0]) {
                translate ([0, 0, 246.80957697923077]) {
                  rotate (a=5.0, v=[0, 1, 0]) {
                    translate ([0, 0, -246.80957697923077]) {
                      translate ([0, 0, 89.18393769497159]) {
                        rotate (a=14.999999999999998, v=[1, 0, 0]) {
                          translate ([0, 0, -89.18393769497159]) {
                            translate ([-8.694999999999999, -8.694999999999999, 0]) {
                              translate ([0, 0, 3]) {
                                cube ([0.01, 0.01, 6], center=true);
                              }
                            }
                          }
                        }
                      }
                    }
                  }
                }
              }
            }
          }
        }
        hull () {
          translate ([0, 0, 30]) {
            rotate (a=40.0, v=[0, 1, 0]) {
              translate ([0, 2.82, -4.5]) {
                translate ([0, 0, 246.80957697923077]) {
                  rotate (a=10.0, v=[0, 1, 0]) {
                    translate ([0, 0, -246.80957697923077]) {
                      translate ([0, 0, 89.18393769497159]) {
                        rotate (a=14.999999999999998, v=[1, 0, 0]) {
                          translate ([0, 0, -89.18393769497159]) {
                            translate ([8.694999999999999, 8.694999999999999, 0]) {
                              translate ([0, 0, 3]) {
                                cube ([0.01, 0.01, 6], center=true);
                              }
                            }
                          }
                        }
                      }
                    }
                  }
                }
              }
            }
          }
          translate ([0, 0, 30]) {
            rotate (a=40.0, v=[0, 1, 0]) {
              translate ([0, 0, 0]) {
                translate ([0, 0, 246.80957697923077]) {
                  rotate (a=5.0, v=[0, 1, 0]) {
                    translate ([0, 0, -246.80957697923077]) {
                      translate ([0, 0, 89.18393769497159]) {
                        rotate (a=14.999999999999998, v=[1, 0, 0]) {
                          translate ([0, 0, -89.18393769497159]) {
                            translate ([-8.694999999999999, -8.694999999999999, 0]) {
                              translate ([0, 0, 3]) {
                                cube ([0.01, 0.01, 6], center=true);
                              }
                            }
                          }
                        }
                      }
                    }
                  }
                }
              }
            }
          }
          translate ([0, 0, 30]) {
            rotate (a=40.0, v=[0, 1, 0]) {
              translate ([0, 2.82, -4.5]) {
                translate ([0, 0, 246.80957697923077]) {
                  rotate (a=10.0, v=[0, 1, 0]) {
                    translate ([0, 0, -246.80957697923077]) {
                      translate ([0, 0, 89.18393769497159]) {
                        rotate (a=14.999999999999998, v=[1, 0, 0]) {
                          translate ([0, 0, -89.18393769497159]) {
                            translate ([8.694999999999999, -8.694999999999999, 0]) {
                              translate ([0, 0, 3]) {
                                cube ([0.01, 0.01, 6], center=true);
                              }
                            }
                          }
                        }
                      }
                    }
                  }
                }
              }
            }
          }
        }
      }
      union () {
        hull () {
          translate ([0, 0, 30]) {
            rotate (a=40.0, v=[0, 1, 0]) {
              translate ([0, 0, 0]) {
                translate ([0, 0, 246.80957697923077]) {
                  rotate (a=5.0, v=[0, 1, 0]) {
                    translate ([0, 0, -246.80957697923077]) {
                      translate ([0, 0, 89.18393769497159]) {
                        rotate (a=0.0, v=[1, 0, 0]) {
                          translate ([0, 0, -89.18393769497159]) {
                            translate ([-8.694999999999999, 8.694999999999999, 0]) {
                              translate ([0, 0, 3]) {
                                cube ([0.01, 0.01, 6], center=true);
                              }
                            }
                          }
                        }
                      }
                    }
                  }
                }
              }
            }
          }
          translate ([0, 0, 30]) {
            rotate (a=40.0, v=[0, 1, 0]) {
              translate ([0, 2.82, -4.5]) {
                translate ([0, 0, 246.80957697923077]) {
                  rotate (a=10.0, v=[0, 1, 0]) {
                    translate ([0, 0, -246.80957697923077]) {
                      translate ([0, 0, 89.18393769497159]) {
                        rotate (a=0.0, v=[1, 0, 0]) {
                          translate ([0, 0, -89.18393769497159]) {
                            translate ([8.694999999999999, 8.694999999999999, 0]) {
                              translate ([0, 0, 3]) {
                                cube ([0.01, 0.01, 6], center=true);
                              }
                            }
                          }
                        }
                      }
                    }
                  }
                }
              }
            }
          }
          translate ([0, 0, 30]) {
            rotate (a=40.0, v=[0, 1, 0]) {
              translate ([0, 0, 0]) {
                translate ([0, 0, 246.80957697923077]) {
                  rotate (a=5.0, v=[0, 1, 0]) {
                    translate ([0, 0, -246.80957697923077]) {
                      translate ([0, 0, 89.18393769497159]) {
                        rotate (a=0.0, v=[1, 0, 0]) {
                          translate ([0, 0, -89.18393769497159]) {
                            translate ([-8.694999999999999, -8.694999999999999, 0]) {
                              translate ([0, 0, 3]) {
                                cube ([0.01, 0.01, 6], center=true);
                              }
                            }
                          }
                        }
                      }
                    }
                  }
                }
              }
            }
          }
        }
        hull () {
          translate ([0, 0, 30]) {
            rotate (a=40.0, v=[0, 1, 0]) {
              translate ([0, 2.82, -4.5]) {
                translate ([0, 0, 246.80957697923077]) {
                  rotate (a=10.0, v=[0, 1, 0]) {
                    translate ([0, 0, -246.80957697923077]) {
                      translate ([0, 0, 89.18393769497159]) {
                        rotate (a=0.0, v=[1, 0, 0]) {
                          translate ([0, 0, -89.18393769497159]) {
                            translate ([8.694999999999999, 8.694999999999999, 0]) {
                              translate ([0, 0, 3]) {
                                cube ([0.01, 0.01, 6], center=true);
                              }
                            }
                          }
                        }
                      }
                    }
                  }
                }
              }
            }
          }
          translate ([0, 0, 30]) {
            rotate (a=40.0, v=[0, 1, 0]) {
              translate ([0, 0, 0]) {
                translate ([0, 0, 246.80957697923077]) {
                  rotate (a=5.0, v=[0, 1, 0]) {
                    translate ([0, 0, -246.80957697923077]) {
                      translate ([0, 0, 89.18393769497159]) {
                        rotate (a=0.0, v=[1, 0, 0]) {
                          translate ([0, 0, -89.18393769497159]) {
                            translate ([-8.694999999999999, -8.694999999999999, 0]) {
                              translate ([0, 0, 3]) {
                                cube ([0.01, 0.01, 6], center=true);
                              }
                            }
                          }
                        }
                      }
                    }
                  }
                }
              }
            }
          }
          translate ([0, 0, 30]) {
            rotate (a=40.0, v=[0, 1, 0]) {
              translate ([0, 2.82, -4.5]) {
                translate ([0, 0, 246.80957697923077]) {
                  rotate (a=10.0, v=[0, 1, 0]) {
                    translate ([0, 0, -246.80957697923077]) {
                      translate ([0, 0, 89.18393769497159]) {
                        rotate (a=0.0, v=[1, 0, 0]) {
                          translate ([0, 0, -89.18393769497159]) {
                            translate ([8.694999999999999, -8.694999999999999, 0]) {
                              translate ([0, 0, 3]) {
                                cube ([0.01, 0.01, 6], center=true);
                              }
                            }
                          }
                        }
                      }
                    }
                  }
                }
              }
            }
          }
        }
      }
      union () {
        hull () {
          translate ([0, 0, 30]) {
            rotate (a=40.0, v=[0, 1, 0]) {
              translate ([0, 0, 0]) {
                translate ([0, 0, 246.80957697923077]) {
                  rotate (a=5.0, v=[0, 1, 0]) {
                    translate ([0, 0, -246.80957697923077]) {
                      translate ([0, 0, 89.18393769497159]) {
                        rotate (a=-14.999999999999998, v=[1, 0, 0]) {
                          translate ([0, 0, -89.18393769497159]) {
                            translate ([-8.694999999999999, 8.694999999999999, 0]) {
                              translate ([0, 0, 3]) {
                                cube ([0.01, 0.01, 6], center=true);
                              }
                            }
                          }
                        }
                      }
                    }
                  }
                }
              }
            }
          }
          translate ([0, 0, 30]) {
            rotate (a=40.0, v=[0, 1, 0]) {
              translate ([0, 2.82, -4.5]) {
                translate ([0, 0, 246.80957697923077]) {
                  rotate (a=10.0, v=[0, 1, 0]) {
                    translate ([0, 0, -246.80957697923077]) {
                      translate ([0, 0, 89.18393769497159]) {
                        rotate (a=-14.999999999999998, v=[1, 0, 0]) {
                          translate ([0, 0, -89.18393769497159]) {
                            translate ([8.694999999999999, 8.694999999999999, 0]) {
                              translate ([0, 0, 3]) {
                                cube ([0.01, 0.01, 6], center=true);
                              }
                            }
                          }
                        }
                      }
                    }
                  }
                }
              }
            }
          }
          translate ([0, 0, 30]) {
            rotate (a=40.0, v=[0, 1, 0]) {
              translate ([0, 0, 0]) {
                translate ([0, 0, 246.80957697923077]) {
                  rotate (a=5.0, v=[0, 1, 0]) {
                    translate ([0, 0, -246.80957697923077]) {
                      translate ([0, 0, 89.18393769497159]) {
                        rotate (a=-14.999999999999998, v=[1, 0, 0]) {
                          translate ([0, 0, -89.18393769497159]) {
                            translate ([-8.694999999999999, -8.694999999999999, 0]) {
                              translate ([0, 0, 3]) {
                                cube ([0.01, 0.01, 6], center=true);
                              }
                            }
                          }
                        }
                      }
                    }
                  }
                }
              }
            }
          }
        }
        hull () {
          translate ([0, 0, 30]) {
            rotate (a=40.0, v=[0, 1, 0]) {
              translate ([0, 2.82, -4.5]) {
                translate ([0, 0, 246.80957697923077]) {
                  rotate (a=10.0, v=[0, 1, 0]) {
                    translate ([0, 0, -246.80957697923077]) {
                      translate ([0, 0, 89.18393769497159]) {
                        rotate (a=-14.999999999999998, v=[1, 0, 0]) {
                          translate ([0, 0, -89.18393769497159]) {
                            translate ([8.694999999999999, 8.694999999999999, 0]) {
                              translate ([0, 0, 3]) {
                                cube ([0.01, 0.01, 6], center=true);
                              }
                            }
                          }
                        }
                      }
                    }
                  }
                }
              }
            }
          }
          translate ([0, 0, 30]) {
            rotate (a=40.0, v=[0, 1, 0]) {
              translate ([0, 0, 0]) {
                translate ([0, 0, 246.80957697923077]) {
                  rotate (a=5.0, v=[0, 1, 0]) {
                    translate ([0, 0, -246.80957697923077]) {
                      translate ([0, 0, 89.18393769497159]) {
                        rotate (a=-14.999999999999998, v=[1, 0, 0]) {
                          translate ([0, 0, -89.18393769497159]) {
                            translate ([-8.694999999999999, -8.694999999999999, 0]) {
                              translate ([0, 0, 3]) {
                                cube ([0.01, 0.01, 6], center=true);
                              }
                            }
                          }
                        }
                      }
                    }
                  }
                }
              }
            }
          }
          translate ([0, 0, 30]) {
            rotate (a=40.0, v=[0, 1, 0]) {
              translate ([0, 2.82, -4.5]) {
                translate ([0, 0, 246.80957697923077]) {
                  rotate (a=10.0, v=[0, 1, 0]) {
                    translate ([0, 0, -246.80957697923077]) {
                      translate ([0, 0, 89.18393769497159]) {
                        rotate (a=-14.999999999999998, v=[1, 0, 0]) {
                          translate ([0, 0, -89.18393769497159]) {
                            translate ([8.694999999999999, -8.694999999999999, 0]) {
                              translate ([0, 0, 3]) {
                                cube ([0.01, 0.01, 6], center=true);
                              }
                            }
                          }
                        }
                      }
                    }
                  }
                }
              }
            }
          }
        }
      }
      union () {
        hull () {
          translate ([0, 0, 30]) {
            rotate (a=40.0, v=[0, 1, 0]) {
              translate ([0, -12, 5.64]) {
                translate ([0, 0, 246.80957697923077]) {
                  rotate (a=0.0, v=[0, 1, 0]) {
                    translate ([0, 0, -246.80957697923077]) {
                      translate ([0, 0, 89.18393769497159]) {
                        rotate (a=14.999999999999998, v=[1, 0, 0]) {
                          translate ([0, 0, -89.18393769497159]) {
                            translate ([-8.694999999999999, 8.694999999999999, 0]) {
                              translate ([0, 0, 3]) {
                                cube ([0.01, 0.01, 6], center=true);
                              }
                            }
                          }
                        }
                      }
                    }
                  }
                }
              }
            }
          }
          translate ([0, 0, 30]) {
            rotate (a=40.0, v=[0, 1, 0]) {
              translate ([0, 0, 0]) {
                translate ([0, 0, 246.80957697923077]) {
                  rotate (a=5.0, v=[0, 1, 0]) {
                    translate ([0, 0, -246.80957697923077]) {
                      translate ([0, 0, 89.18393769497159]) {
                        rotate (a=14.999999999999998, v=[1, 0, 0]) {
                          translate ([0, 0, -89.18393769497159]) {
                            translate ([8.694999999999999, 8.694999999999999, 0]) {
                              translate ([0, 0, 3]) {
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
