atsuyuki/dactyl-manuform-skeleton-edition-4x5/source/things/right_baseplate.scad

linear_extrude(4)import("right_baseplate.svg");
