atsuyuki/dactyl-manuform-skeleton-edition-4x5/source/things/test.scad

difference () {
  translate ([-63.991374938052125, 42.578110478055464, 8.8]) {
    cube ([10.5, 10.0, 17.6], center=true);
  }
  translate ([-63.991374938052125, 42.578110478055464, 8.8]) {
    cube ([6.5, 10.0, 13.6], center=true);
  }
}
